danielmader/MatrixClock_MicroPythonESP/src/characters.py

# noqa: E231

big0 = [
    [0,1,1,1,1,1,1,0],
    [1,1,1,1,1,1,1,1],
    [1,1,0,0,0,0,1,1],
    [1,1,0,0,0,0,1,1],
    [1,1,0,0,0,0,1,1],
    [1,1,0,0,0,0,1,1],
    [1,1,0,0,0,0,1,1],
    [1,1,0,0,0,0,1,1],
    [1,1,0,0,0,0,1,1],
    [1,1,0,0,0,0,1,1],
    [1,1,0,0,0,0,1,1],
    [1,1,0,0,0,0,1,1],
    [1,1,1,1,1,1,1,1],
    [0,1,1,1,1,1,1,0],
    ]

big1 = [
    [0,0,0,1,1,0,0,0],
    [0,0,1,1,1,0,0,0],
    [0,1,1,1,1,0,0,0],
    [0,0,0,1,1,0,0,0],
    [0,0,0,1,1,0,0,0],
    [0,0,0,1,1,0,0,0],
    [0,0,0,1,1,0,0,0],
    [0,0,0,1,1,0,0,0],
    [0,0,0,1,1,0,0,0],
    [0,0,0,1,1,0,0,0],
    [0,0,0,1,1,0,0,0],
    [0,0,0,1,1,0,0,0],
    [1,1,1,1,1,1,1,1],
    [1,1,1,1,1,1,1,1],
    ]

big2 = [
    [0,1,1,1,1,1,1,0],
    [1,1,1,1,1,1,1,1],
    [1,1,0,0,0,0,1,1],
    [0,0,0,0,0,0,1,1],
    [0,0,0,0,0,0,1,1],
    [0,0,0,0,0,0,1,1],
    [0,0,0,0,0,1,1,0],
    [0,0,0,0,1,1,0,0],
    [0,0,0,1,1,0,0,0],
    [0,0,1,1,0,0,0,0],
    [0,1,1,0,0,0,0,0],
    [1,1,0,0,0,0,0,0],
    [1,1,1,1,1,1,1,1],
    [1,1,1,1,1,1,1,1],
    ]

big3 = [
    [0,1,1,1,1,1,1,0],
    [1,1,1,1,1,1,1,1],
    [1,1,0,0,0,0,1,1],
    [0,0,0,0,0,0,1,1],
    [0,0,0,0,0,0,1,1],
    [0,0,0,0,0,0,1,1],
    [0,0,0,0,1,1,1,0],
    [0,0,0,0,1,1,1,0],
    [0,0,0,0,0,0,1,1],
    [0,0,0,0,0,0,1,1],
    [0,0,0,0,0,0,1,1],
    [1,1,0,0,0,0,1,1],
    [1,1,1,1,1,1,1,1],
    [0,1,1,1,1,1,1,0],
    ]

big4 = [
    [1,1,0,0,0,0,0,0],
    [1,1,0,0,0,0,0,0],
    [1,1,0,0,0,0,0,0],
    [1,1,0,0,0,0,0,0],
    [1,1,0,0,0,0,0,0],
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
    [0],
    [0],
    ]

small_degree = [
    [0,1,0],
    [1,0,1],
    [0,1,0],
    [0,0,0],
    [0,0,0],
    [0,0,0],
    [0,0,0],
    ]

small_degreeC = [
    [0,1,0,1,1,1],
    [1,0,1,1,0,0],
    [0,1,0,1,0,0],
    [0,0,0,1,1,1],
    [0,0,0,0,0,0],
    [0,0,0,0,0,0],
    [0,0,0,0,0,0],
    ]

small_percent = [
    [0,0,0,0,0],
    [0,0,0,0,0],
    [0,1,0,0,1],
    [0,0,0,1,0],
    [0,0,1,0,0],
    [0,1,0,0,1],
    [0,0,0,0,0],
    ]

small_dash = [
    [0,0,0,0],
    [0,0,0,0],
    [0,0,0,0],
    [1,1,1,1],
    [0,0,0,0],
    [0,0,0,0],
    [0,0,0,0],
    ]

small_space = [
    [0,0,0,0,0],
    [0,0,0,0,0],
    [0,0,0,0,0],
    [0,0,0,0,0],
    [0,0,0,0,0],
    [0,0,0,0,0],
    [0,0,0,0,0],
    ]

##*****************************************************************************
##*****************************************************************************

pixel_black = [
    [0],
    ]

pixel_blue = [
    [1],
    ]
